corneliusmunz/FxWind/auto_firmware_version.py

import subprocess

Import("env")

def get_firmware_specifier_build_flag():    
    ret = subprocess.run(["git", "describe", "--tags", "--long"], stdout=subprocess.PIPE, text=True) 
    build_version = ret.stdout.strip()
    build_flag = "-D FWVERSION=\\\"" + build_version + "\\\""
    print ("Firmware Revision: " + build_version)
    return (build_flag)

env.Append(
    BUILD_FLAGS=[get_firmware_specifier_build_flag()]
)
